SimonMeersschaut/Chocolate-Printer/documentation/links/599c34ea-fc0d-46fc-8a5a-dea9c5af7767.png

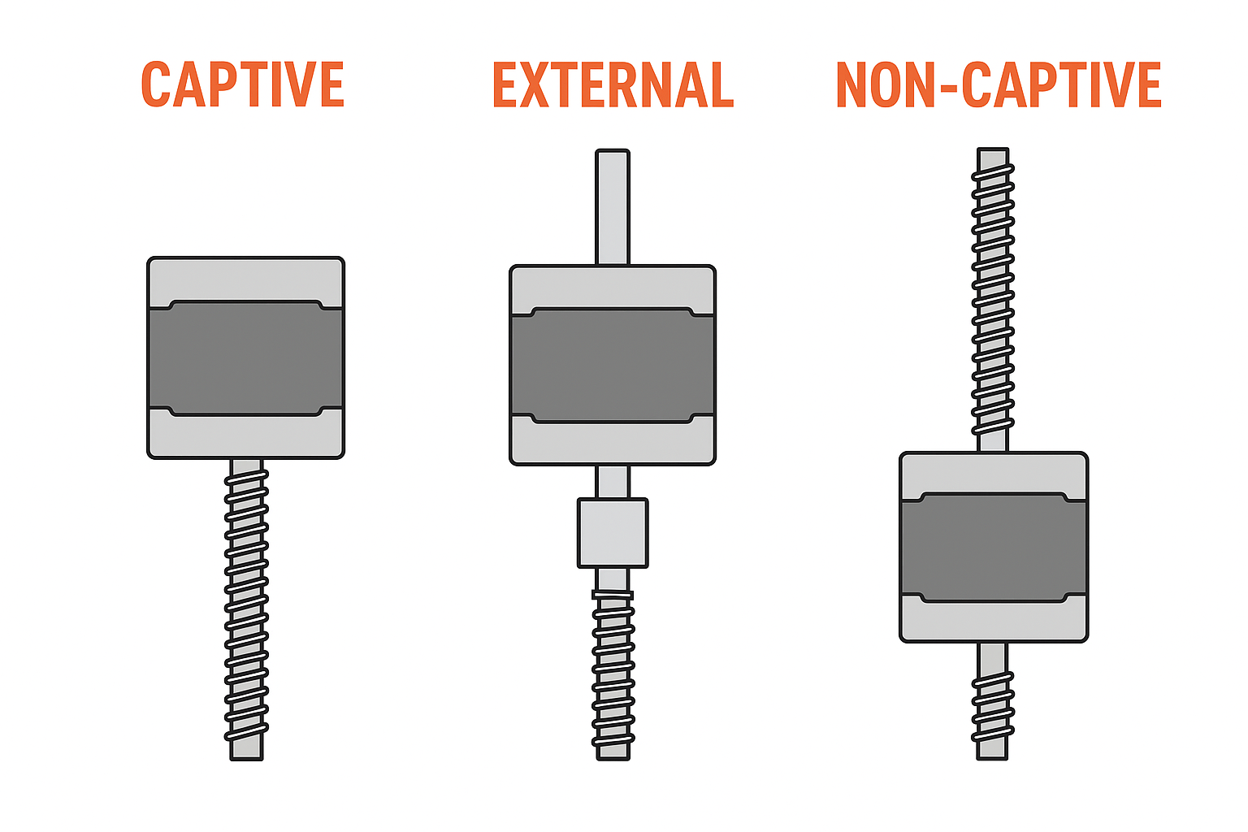
documentation/links/599c34ea-fc0d-46fc-8a5a-dea9c5af7767.png
