SimonMeersschaut/Chocolate-Printer/documentation/links/IMG_7886.jpg

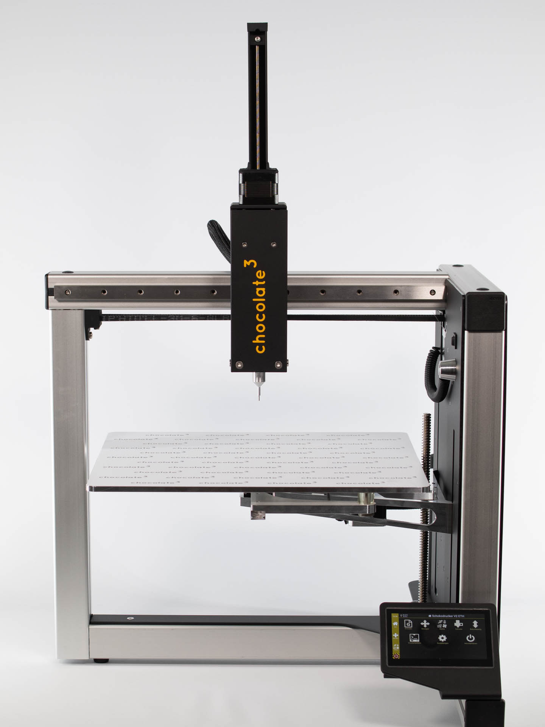
documentation/links/IMG_7886.jpg
