SimonMeersschaut/Chocolate-Printer/documentation/links/Screenshot 2025-09-05 110448.png

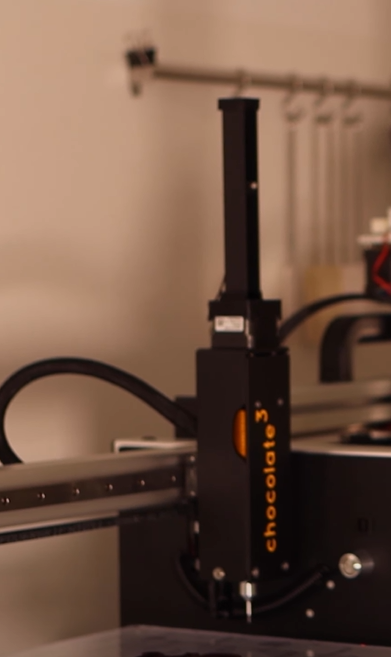
documentation/links/Screenshot 2025-09-05 110448.png
