SimonMeersschaut/Chocolate-Printer/documentation/hardware/stepper_motor/step_calibration.png

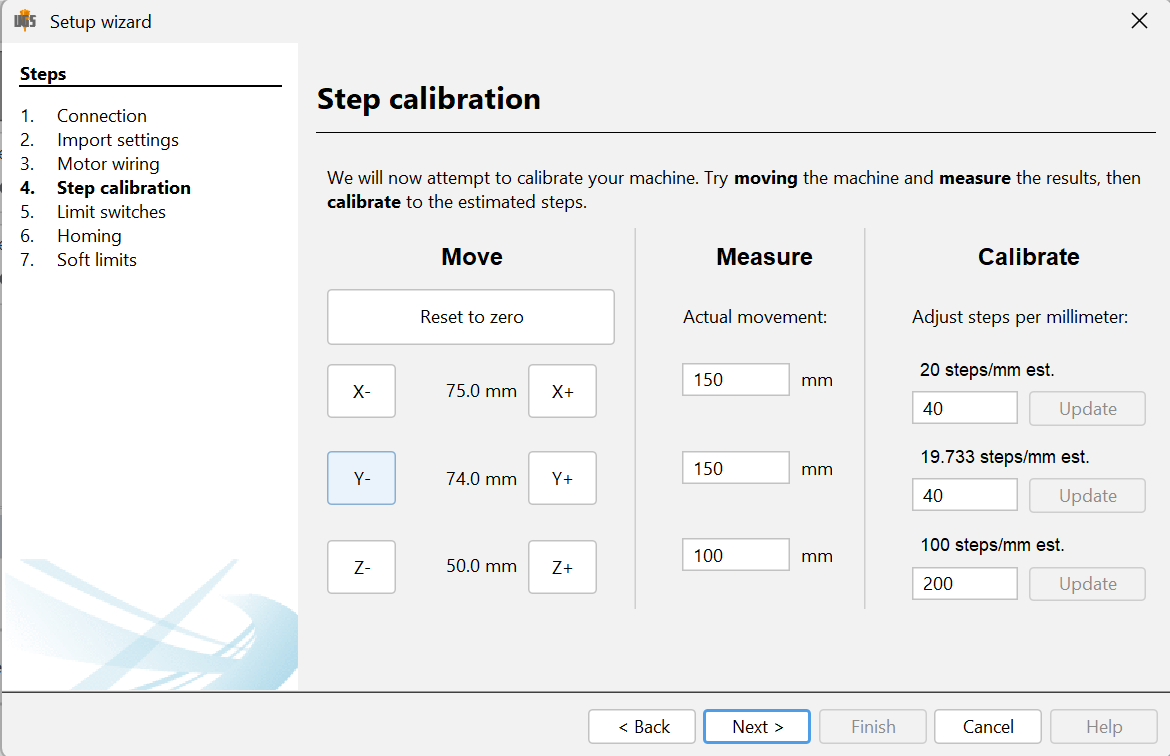
documentation/hardware/stepper_motor/step_calibration.png
